ihsanalhafiz/Bajo_Board/Hardware_Part/schematic.sch

## EAGLE design Hardware_Part/schematic.sch (2023-11-11)

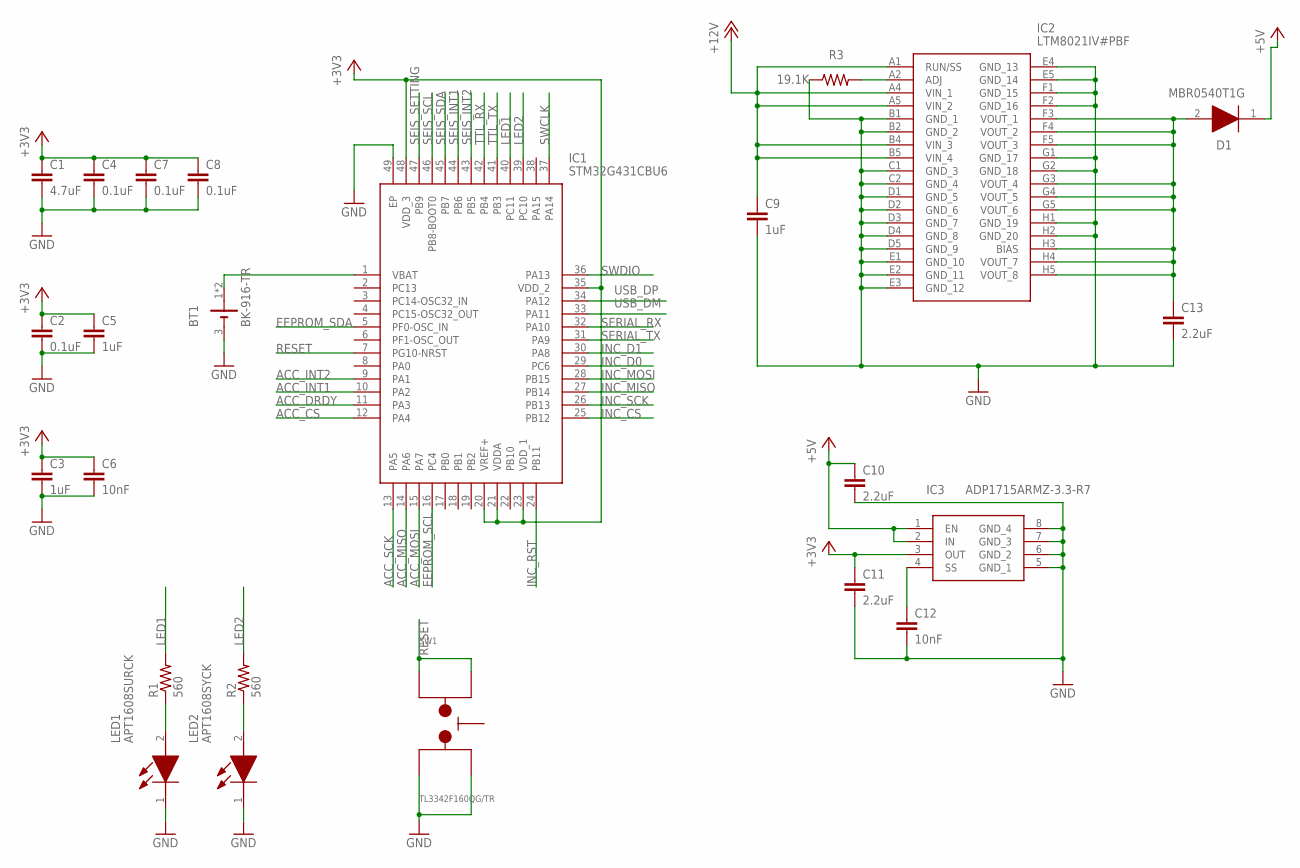
[picture p10: schematic schematic.sch, sheet 1]

Parts:
BT1: BK-916-TR; BAT_BK-916-TR; MANUFACTURERPARTNUMBER BK-916-TR
C1: 4.7uF; CAPC1608X80N-0603-KEMET; MANUFACTURERPARTNUMBER C0603C475K9PACTU
C2, C4, C7, C8: 0.1uF; CAPC1005X50N-0402-KEMET; MANUFACTURERPARTNUMBER C0402C104K4RACTU
C3, C5: 1uF; CAPC1005X50N-0402-KEMET; MANUFACTURERPARTNUMBER CC0402KRX5R5BB105
C6: 10nF; CAPC1005X50N-0402-KEMET; MANUFACTURERPARTNUMBER C0402C103K3RACTU
C9: 1uF; CAPC2113X90N-0805-KEMET; MANUFACTURERPARTNUMBER C0805C105K5RACTU
C10, C11: 2.2uF; CAPC1608X80N-0603-KEMET; MANUFACTURERPARTNUMBER C1608X5R1C225K080AB
C12: 10nF; CAPC1005X50N-0402-KEMET; MANUFACTURERPARTNUMBER CC0402KRX7R7BB103
C13: 2.2uF; CAPC2113X90N-0805-KEMET; MANUFACTURERPARTNUMBER C0805C225K8RACTU
D1: MBR0540T1G; SOD3716X135N; MANUFACTURERPARTNUMBER MBR0540T1G
IC1: STM32G431CBU6; QFN50P700X700X65-49N; MANUFACTURERPARTNUMBER STM32G431CBU6
IC2: LTM8021IV#PBF; LTM8021IVPBF; MANUFACTURERPARTNUMBER LTM8021IV#PBF
IC3: ADP1715ARMZ-3.3-R7; SOP65P490X110-8N; MANUFACTURERPARTNUMBER ADP1715ARMZ-3.3-R7
LED1: APT1608SURCK; LEDC1608X85N; MANUFACTURERPARTNUMBER APT1608SURCK
LED2: APT1608SYCK; LEDC1608X85N; MANUFACTURERPARTNUMBER APT1608SYCK
R1, R2: 560; RESC1005X30N; MANUFACTURERPARTNUMBER RCS0402560RFKED
R3: 19.1K; RESC1005X30N; MANUFACTURERPARTNUMBER ERJ-2RKF1912X
SW1: TL3342F160QG/TR; MANUFACTURERPARTNUMBER TL3342F160QG/TR

Connections:
+3V3: C1.1, C2.1, C3.1, C4.1, C5.1, C6.1, C7.1, C8.1, C11.1, IC1.20 (VREF+), IC1.21 (VDDA), IC1.23 (VDD_1), IC1.35 (VDD_2), IC1.48 (VDD_3), IC3.3 (OUT)
+5V: C10.1, D1.1 (K), IC3.1 (EN), IC3.2 (IN)
+12V: C9.1, IC2.A1 (RUN/SS), IC2.A4 (VIN_1), IC2.A5 (VIN_2), IC2.B4 (VIN_3), IC2.B5 (VIN_4)
ACC_CS: IC1.12 (PA4)
ACC_DRDY: IC1.11 (PA3)
ACC_INT1: IC1.10 (PA2)
ACC_INT2: IC1.9 (PA1)
ACC_MISO: IC1.14 (PA6)
ACC_MOSI: IC1.15 (PA7)
ACC_SCK: IC1.13 (PA5)
EEPROM_SCL: IC1.16 (PC4)
EEPROM_SDA: IC1.5 (PF0-OSC_IN)
GND: BT1.3 (-), C1.2, C2.2, C3.2, C4.2, C5.2, C6.2, C7.2, C8.2, C9.2, C10.2, C11.2, C12.2, C13.2, IC1.49 (EP), IC2.B1 (GND_1), IC2.B2 (GND_2), IC2.C1 (GND_3), IC2.C2 (GND_4), IC2.D1 (GND_5), IC2.D2 (GND_6), IC2.D3 (GND_7), IC2.D4 (GND_8), IC2.D5 (GND_9), IC2.E1 (GND_10), IC2.E2 (GND_11), IC2.E3 (GND_12), IC2.E4 (GND_13), IC2.E5 (GND_14), IC2.F1 (GND_15), IC2.F2 (GND_16), IC2.G1 (GND_17), IC2.G2 (GND_18), IC2.H1 (GND_19), IC2.H2 (GND_20), IC3.5 (GND_1), IC3.6 (GND_2), IC3.7 (GND_3), IC3.8 (GND_4), LED1.1 (K), LED2.1 (K), R3.1, SW1.1, SW1.2
INC_CS: IC1.25 (PB12)
INC_D0: IC1.29 (PC6)
INC_D1: IC1.30 (PA8)
INC_MISO: IC1.27 (PB14)
INC_MOSI: IC1.28 (PB15)
INC_RST: IC1.24 (PB11)
INC_SCK: IC1.26 (PB13)
LED1: IC1.40 (PC11), R1.2
LED2: IC1.39 (PC10), R2.2
unnamed: C13.1, D1.2 (A), IC2.F3 (VOUT_1), IC2.F4 (VOUT_2), IC2.F5 (VOUT_3), IC2.G3 (VOUT_4), IC2.G4 (VOUT_5), IC2.G5 (VOUT_6), IC2.H3 (BIAS), IC2.H4 (VOUT_7), IC2.H5 (VOUT_8)
unnamed: BT1.1 (+), IC1.1 (VBAT)
unnamed: IC2.A2 (ADJ), R3.2
unnamed: C12.1, IC3.4 (SS)
unnamed: LED1.2 (A), R1.1
unnamed: LED2.2 (A), R2.1
RESET: IC1.7 (PG10-NRST), SW1.3, SW1.4
SEIS_INT1: IC1.44 (PB6)
SEIS_INT2: IC1.43 (PB5)
SEIS_SCL: IC1.46 (PB8-BOOT0)
SEIS_SDA: IC1.45 (PB7)
SEIS_SETTING: IC1.47 (PB9)
SERIAL_RX: IC1.32 (PA10)
SERIAL_TX: IC1.31 (PA9)
SWCLK: IC1.37 (PA14)
SWDIO: IC1.36 (PA13)
TTL_RX: IC1.42 (PB4)
TTL_TX: IC1.41 (PB3)
USB_DM: IC1.33 (PA11)
USB_DP: IC1.34 (PA12)

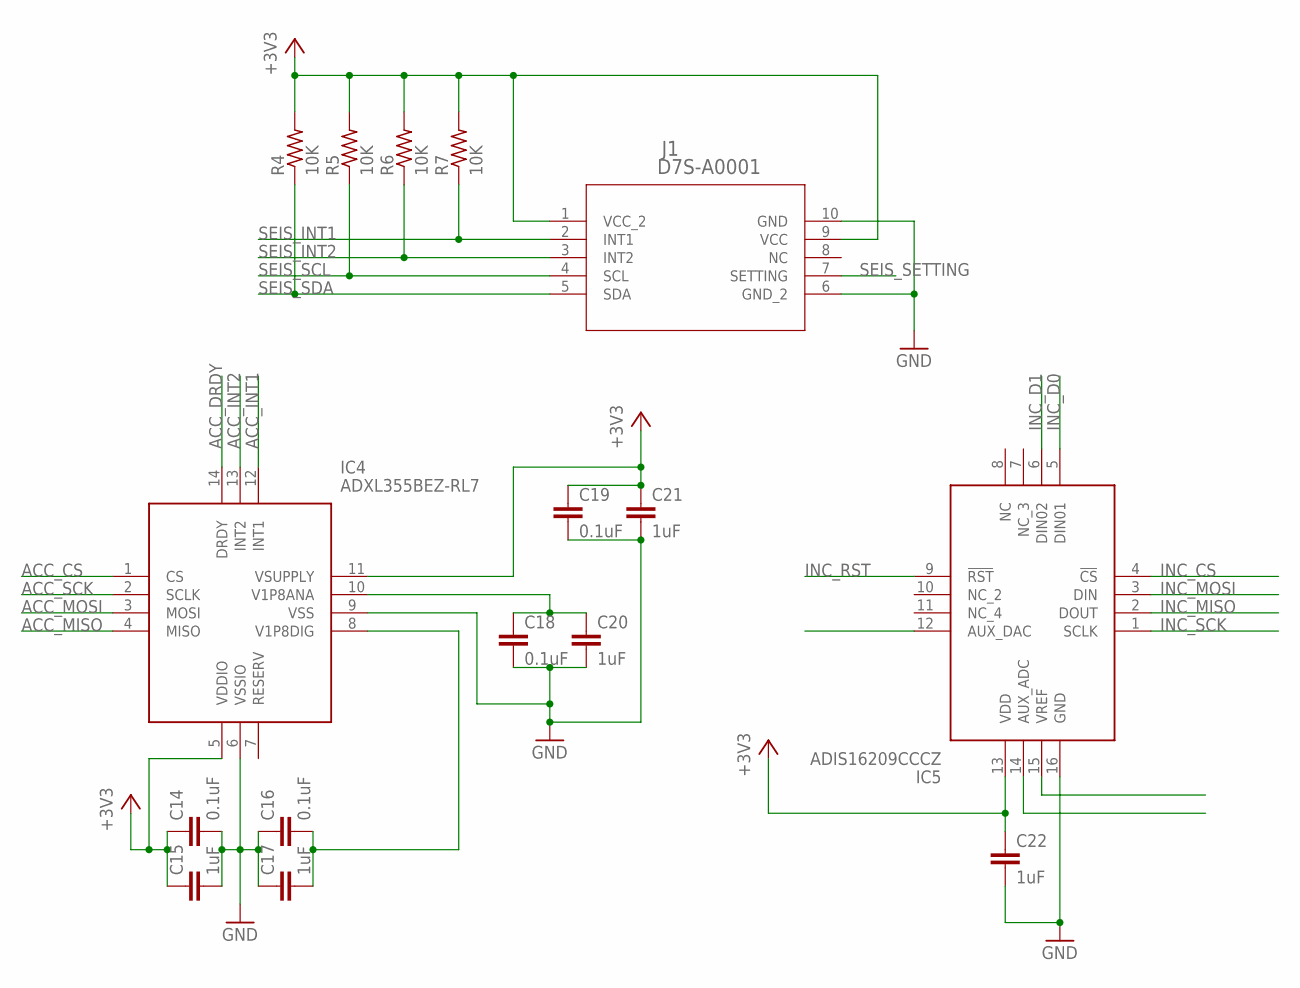
[picture p11: schematic schematic.sch, sheet 2]

Parts:
C14, C16, C18, C19: 0.1uF; CAPC1005X50N-0402-KEMET; MANUFACTURERPARTNUMBER C0402C104K4RACTU
C15, C17, C20, C21: 1uF; CAPC1005X50N-0402-KEMET; MANUFACTURERPARTNUMBER CC0402KRX5R5BB105
C22: 1uF; CAPC1005X50N-0402-KEMET; MANUFACTURERPARTNUMBER CGA2B1X7R1C104K050BC
IC4: ADXL355BEZ-RL7; ADXL355BEZRL7; MANUFACTURERPARTNUMBER ADXL355BEZ-RL7
IC5: ADIS16209CCCZ; LGA16R180P4X4_933X933X390; MANUFACTURERPARTNUMBER ADIS16209CCCZ
J1: D7S-A0001; D7S-A0001_OMR; MANUFACTURERPARTNUMBER D7S-A0001
R4, R5, R6, R7: 10K; RESC1005X30N; MANUFACTURERPARTNUMBER RC0402FR-0710KL

Connections:
+3V3: C14.1, C15.1, C19.1, C21.1, C22.1, IC4.5 (VDDIO), IC4.11 (VSUPPLY), IC5.13 (VDD), J1.1 (VCC_2), J1.9 (VCC), R4.2, R5.2, R6.2, R7.2
ACC_CS: IC4.1 (CS)
ACC_DRDY: IC4.14 (DRDY)
ACC_INT1: IC4.12 (INT1)
ACC_INT2: IC4.13 (INT2)
ACC_MISO: IC4.4 (MISO)
ACC_MOSI: IC4.3 (MOSI)
ACC_SCK: IC4.2 (SCLK)
GND: C14.2, C15.2, C16.1, C17.1, C18.2, C19.2, C20.2, C21.2, C22.2, IC4.6 (VSSIO), IC4.9 (VSS), IC5.16 (GND), J1.6 (GND_2), J1.10 (GND)
INC_CS: IC5.4 (!CS)
INC_D0: IC5.5 (DIN01)
INC_D1: IC5.6 (DIN02)
INC_MISO: IC5.2 (DOUT)
INC_MOSI: IC5.3 (DIN)
INC_RST: IC5.9 (!RST)
INC_SCK: IC5.1 (SCLK)
unnamed: C16.2, C17.2, IC4.8 (V1P8DIG)
unnamed: C18.1, C20.1, IC4.10 (V1P8ANA)
SEIS_INT1: J1.2 (INT1), R7.1
SEIS_INT2: J1.3 (INT2), R6.1
SEIS_SCL: J1.4 (SCL), R5.1
SEIS_SDA: J1.5 (SDA), R4.1
SEIS_SETTING: J1.7 (SETTING)

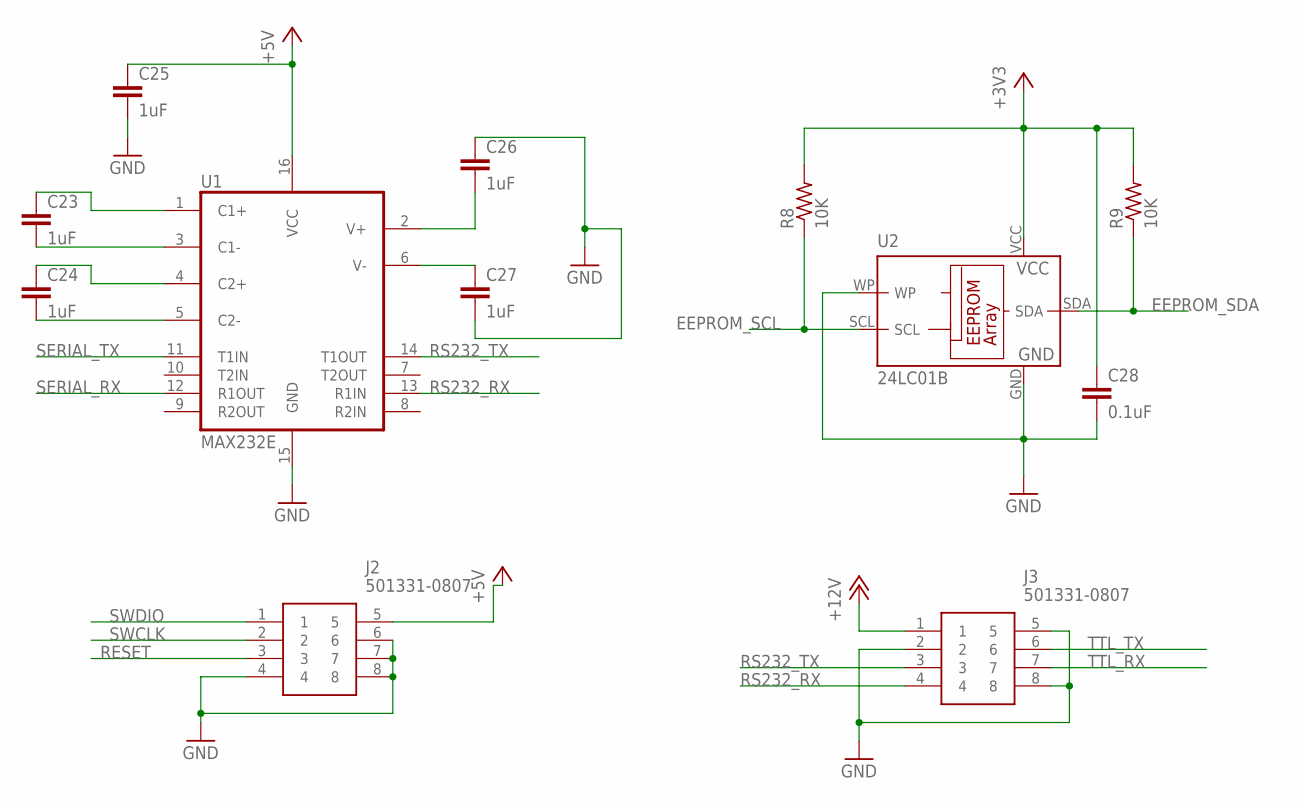
[picture p12: schematic schematic.sch, sheet 3]

Parts:
C23, C24, C25, C26, C27: 1uF; CAPC1608X80N-0603-KEMET; MANUFACTURERPARTNUMBER CGA3E1X7R1C105K080AC
C28: 0.1uF; CAPC1005X50N-0402-KEMET; MANUFACTURERPARTNUMBER C0402C104Z4VAC7867
J2, J3: 501331-0807; MANUFACTURERPARTNUMBER 5013310807
R8, R9: 10K; RESC1005X35N-0402-VISHAYDALE; MANUFACTURERPARTNUMBER RC0402FR-0710KL
U1: MAX232E; SOIC127P1030X265-16N; MANUFACTURERPARTNUMBER MAX232ECDW
U2: 24LC01B; SOT23-5L; MANUFACTURERPARTNUMBER 24LC01BT-I/OT

Connections:
+3V3: C28.1, R8.2, R9.2, U2.VCC
+5V: C25.1, J2.5, U1.16 (VCC)
+12V: J3.1
EEPROM_SCL: R8.1, U2.SCL
EEPROM_SDA: R9.1, U2.SDA
GND: C25.2, C26.1, C27.2, C28.2, J2.4, J2.6, J2.7, J2.8, J3.2, J3.5, J3.8, U1.15 (GND), U2.GND, U2.WP
unnamed: C23.1, U1.1 (C1+)
unnamed: C23.2, U1.3 (C1-)
unnamed: C24.1, U1.4 (C2+)
unnamed: C24.2, U1.5 (C2-)
unnamed: C26.2, U1.2 (V+)
unnamed: C27.1, U1.6 (V-)
RESET: J2.3
RS232_RX: J3.4, U1.13 (R1IN)
RS232_TX: J3.3, U1.14 (T1OUT)
SERIAL_RX: U1.12 (R1OUT)
SERIAL_TX: U1.11 (T1IN)
SWCLK: J2.2
SWDIO: J2.1
TTL_RX: J3.7
TTL_TX: J3.6
